Phunkafizer/RFM-gateway/Firmware/include/main.h

#pragma once

#include <PubSubClient.h>
#include <ESPAsyncWebServer.h>
#include "rfm.h"

extern PubSubClient mqtt;
extern AsyncWebSocket ws;
extern String baseTopic;
extern Rfm69 *rfm69;
extern AsyncWebServer websrv;
extern PGM_P APP_JSON;

extern String getAvailabilityTopic();
