Phunkafizer/RFM-gateway/Firmware/src/applications/fs20.cpp

#include "fs20.h"

FS20::FS20(const JsonObject &conf):
        RcPulseTransceiver(868350000UL, 863000000UL, 870000000UL) {
    (void) conf;
    new FS20Codec;
}

FS20::~FS20() {
    RcCodec::freeCodecs();
}
